MOSH-Insa-Toulouse/2024-2025-4GP-cookingmae-MaouLidaDev/Simulation sous LTSpice/Circuit Capteur complet avec bruit.asc

C1: cap; 100n
C2: cap; 100n
C3: cap; 0.001p
C4: cap; 1µ
R1: res; 100k
R2: res; 1k
R3: res; 100k
R5: res; 10K; tol=1 pwr=0.1
R6: res; 1k
U1: LTC1050
V1: voltage; 5
V2: voltage; PULSE(0 1 0.2 0.1 0.1 20); AC 1
V3: voltage; SINE(0 325 50)
X1: Symbolique
Named nets: 0, ADC
.tran 2
